VoiciD/System-for-recieving-geostationary-satellites-by-the-IAT-Groundstation/doc/Bilder/CW Basisband.png

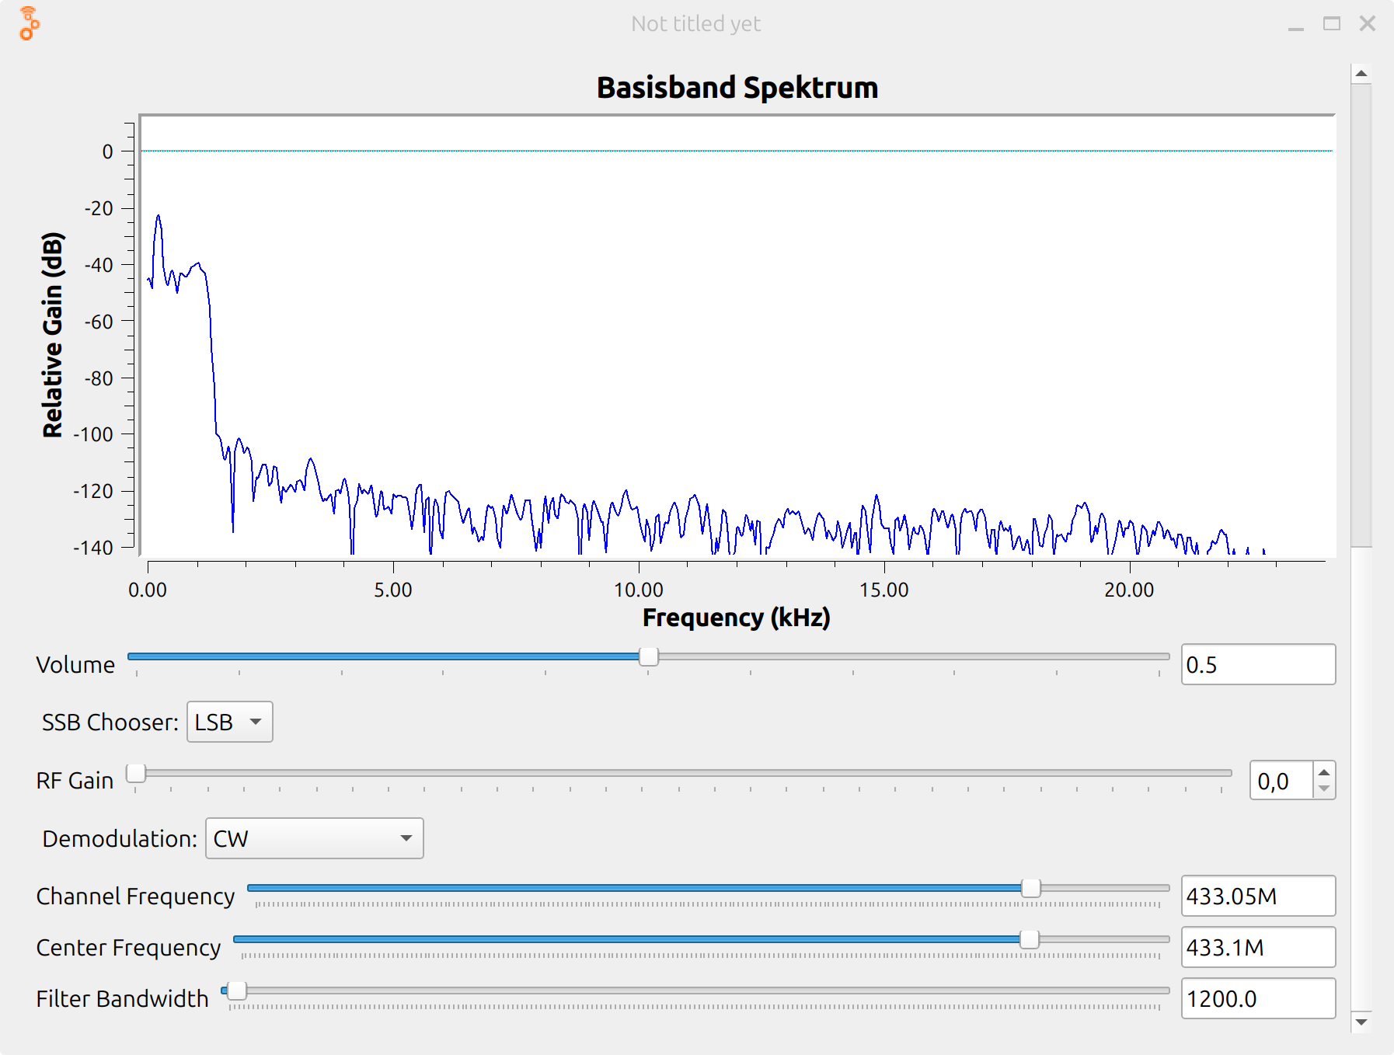
doc/Bilder/CW Basisband.png
