VoiciD/System-for-recieving-geostationary-satellites-by-the-IAT-Groundstation/doc/Bilder/Duobandfeed.jpg

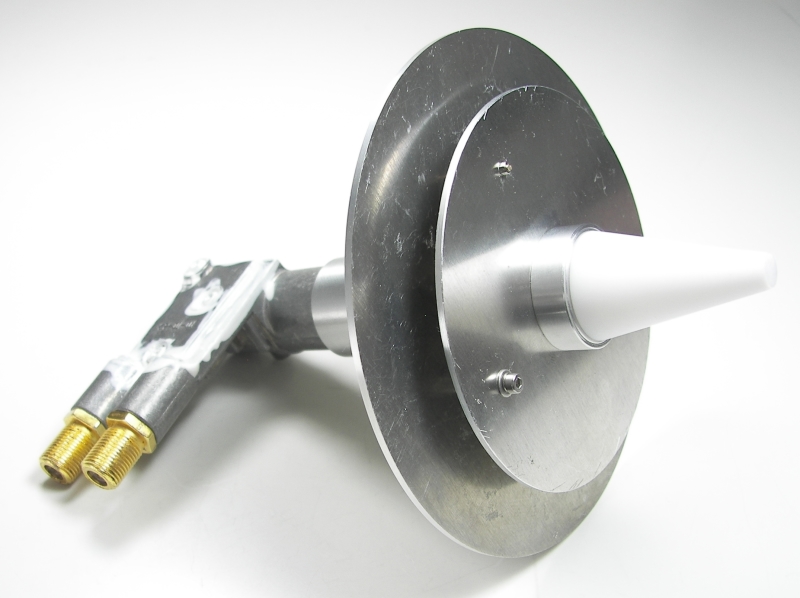
doc/Bilder/Duobandfeed.jpg
