VoiciD/System-for-recieving-geostationary-satellites-by-the-IAT-Groundstation/doc/Bilder/FM Radio.png

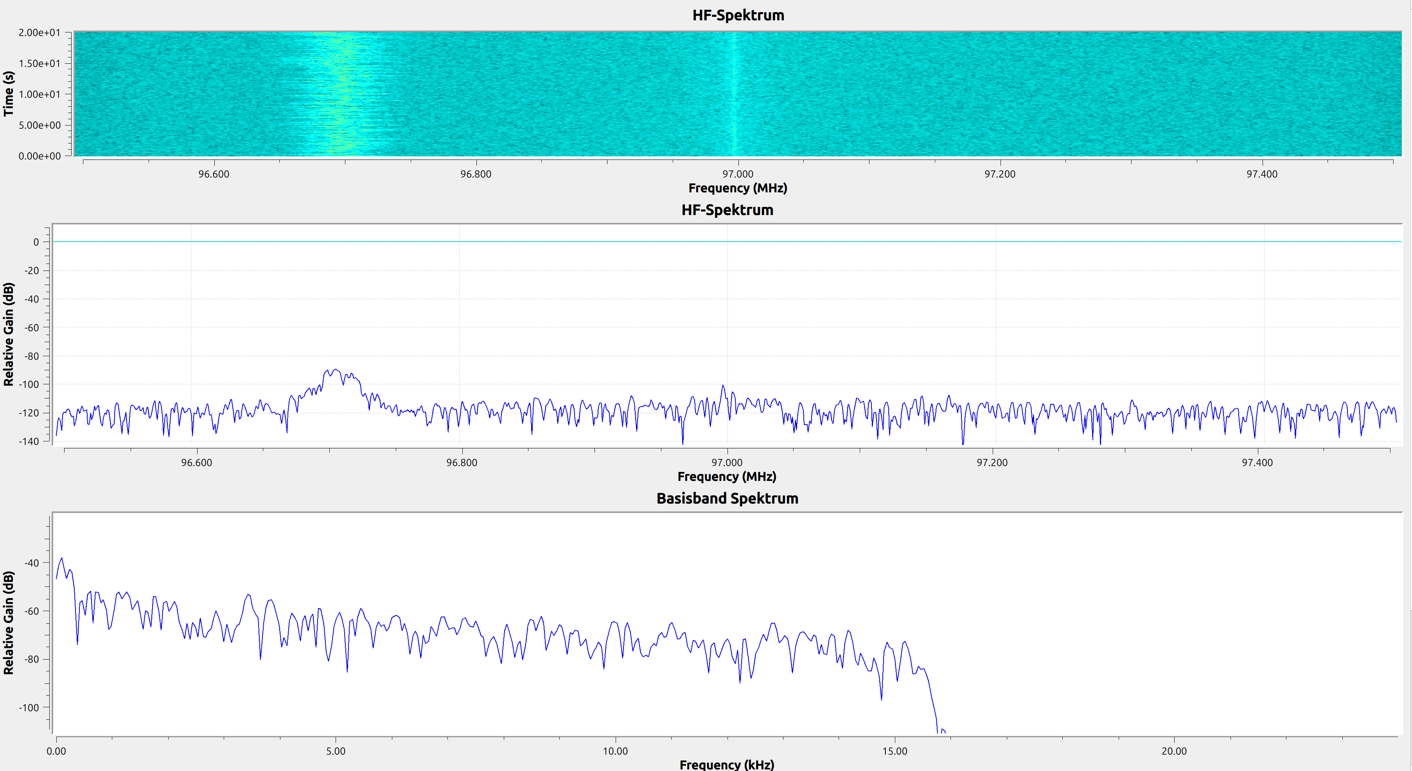
doc/Bilder/FM Radio.png
