VoiciD/System-for-recieving-geostationary-satellites-by-the-IAT-Groundstation/doc/Bilder/HF-Spektrum LSB.png

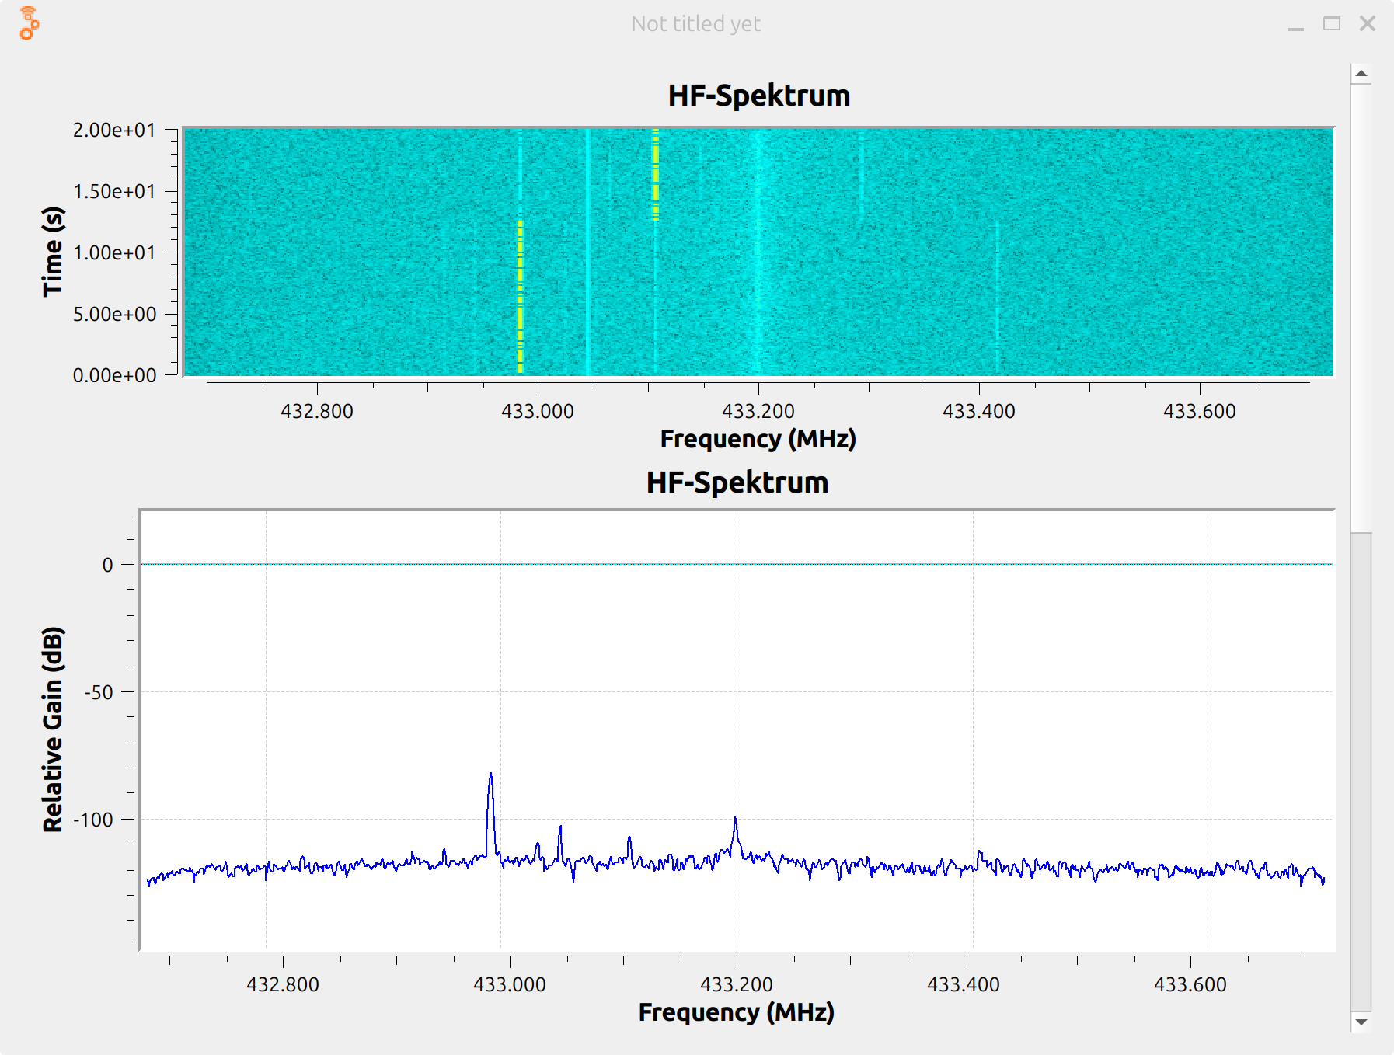
doc/Bilder/HF-Spektrum LSB.png
