VoiciD/System-for-recieving-geostationary-satellites-by-the-IAT-Groundstation/doc/Bilder/KU BT 10 REF.png

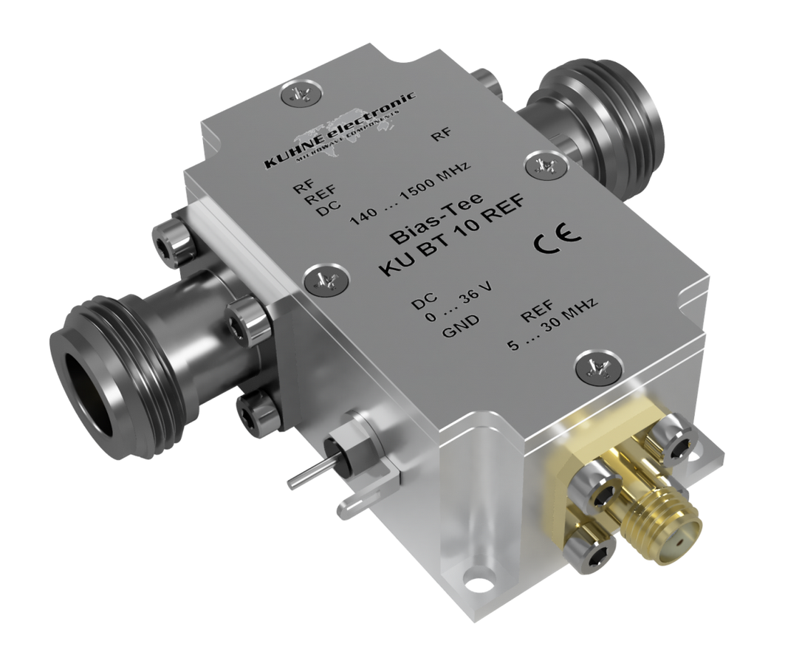
doc/Bilder/KU BT 10 REF.png
