VoiciD/System-for-recieving-geostationary-satellites-by-the-IAT-Groundstation/doc/Bilder/LinkBudget_lightRain.png

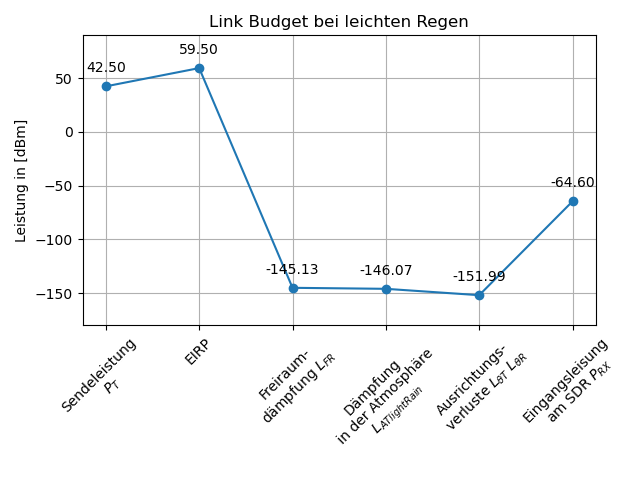
doc/Bilder/LinkBudget_lightRain.png
