VoiciD/System-for-recieving-geostationary-satellites-by-the-IAT-Groundstation/doc/Bilder/LSB Basisband.png

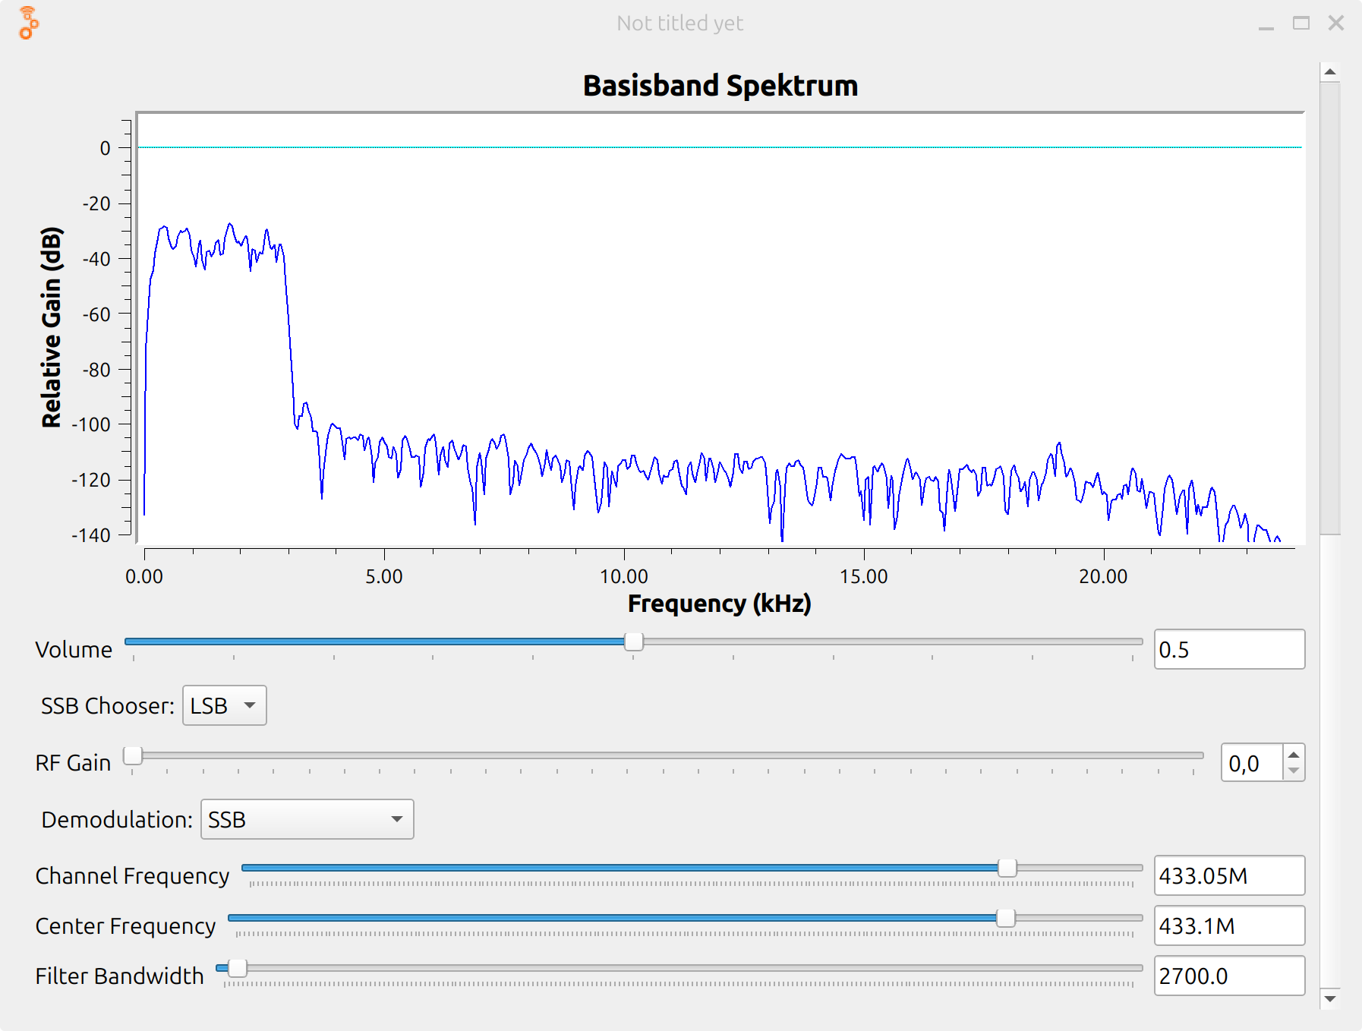
doc/Bilder/LSB Basisband.png
