VoiciD/System-for-recieving-geostationary-satellites-by-the-IAT-Groundstation/doc/Bilder/MKU LNC10 QO 100.png

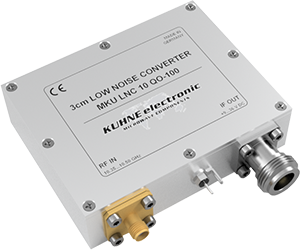
doc/Bilder/MKU LNC10 QO 100.png
