VoiciD/System-for-recieving-geostationary-satellites-by-the-IAT-Groundstation/Grafiken/Bilder/Aufgebaute Antenne.jpg

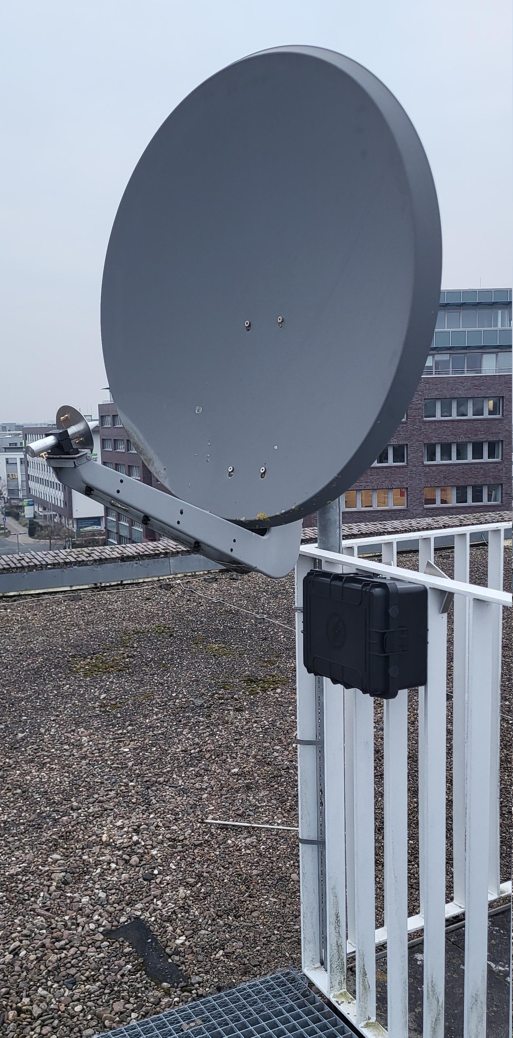
Grafiken/Bilder/Aufgebaute Antenne.jpg
