VoiciD/System-for-recieving-geostationary-satellites-by-the-IAT-Groundstation/Grafiken/Bilder/Gedruckter Feedhalter.jpg

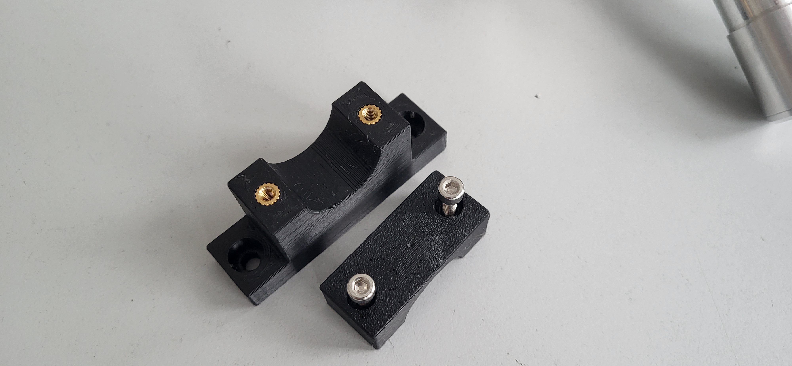
Grafiken/Bilder/Gedruckter Feedhalter.jpg
