VoiciD/System-for-recieving-geostationary-satellites-by-the-IAT-Groundstation/Grafiken/Bilder/Gelieferter Triplebandfeed.jpg

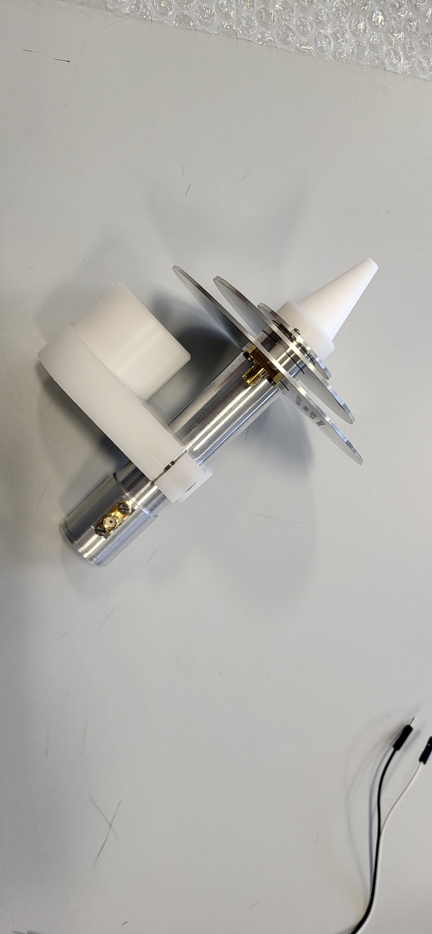
Grafiken/Bilder/Gelieferter Triplebandfeed.jpg
