VoiciD/System-for-recieving-geostationary-satellites-by-the-IAT-Groundstation/Grafiken/Bilder/LNC im Gehäuse.jpg

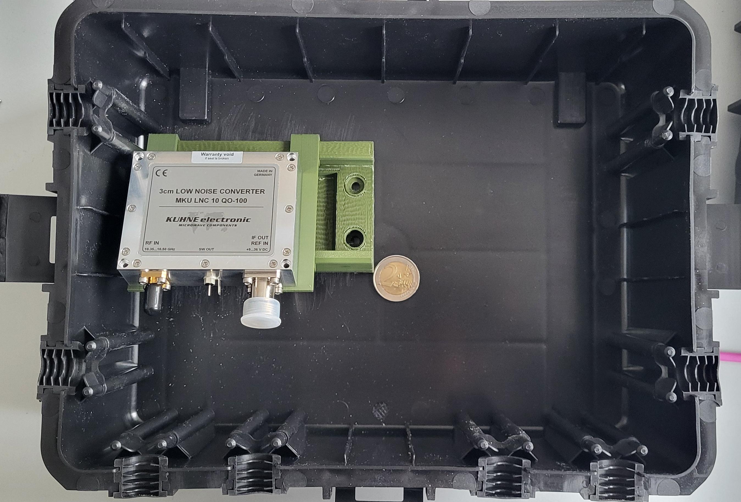
Grafiken/Bilder/LNC im Gehäuse.jpg
