VoiciD/System-for-recieving-geostationary-satellites-by-the-IAT-Groundstation/Grafiken/Bilder/RF-Switch und Patchfeld.jpg

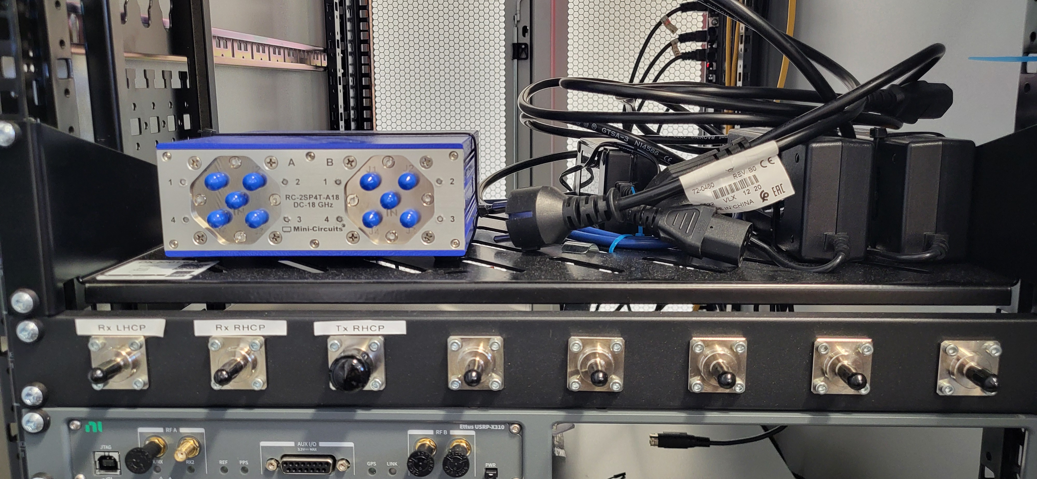
Grafiken/Bilder/RF-Switch und Patchfeld.jpg
