VoiciD/System-for-recieving-geostationary-satellites-by-the-IAT-Groundstation/Grafiken/Bilder/Vorhandene Antenne.jpg

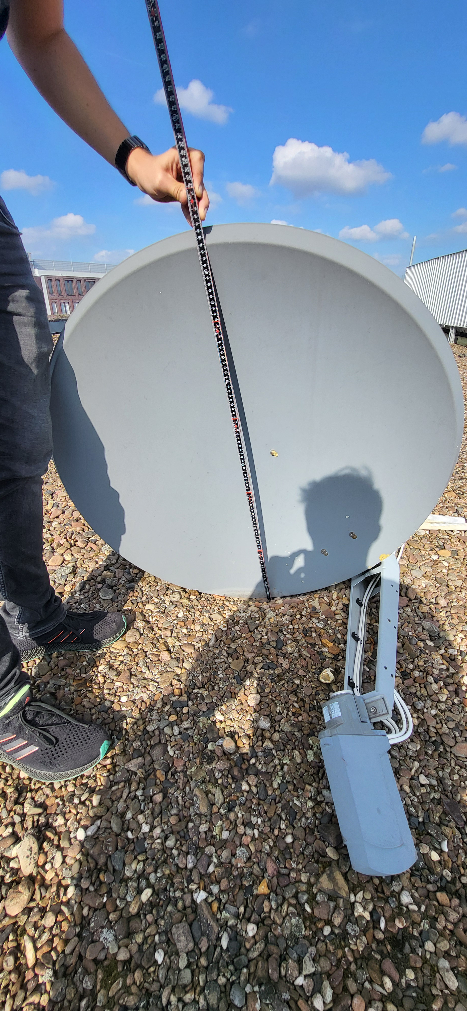
Grafiken/Bilder/Vorhandene Antenne.jpg
