VoiciD/System-for-recieving-geostationary-satellites-by-the-IAT-Groundstation/Grafiken/Messungen/Spektrum EsHail-2.PNG

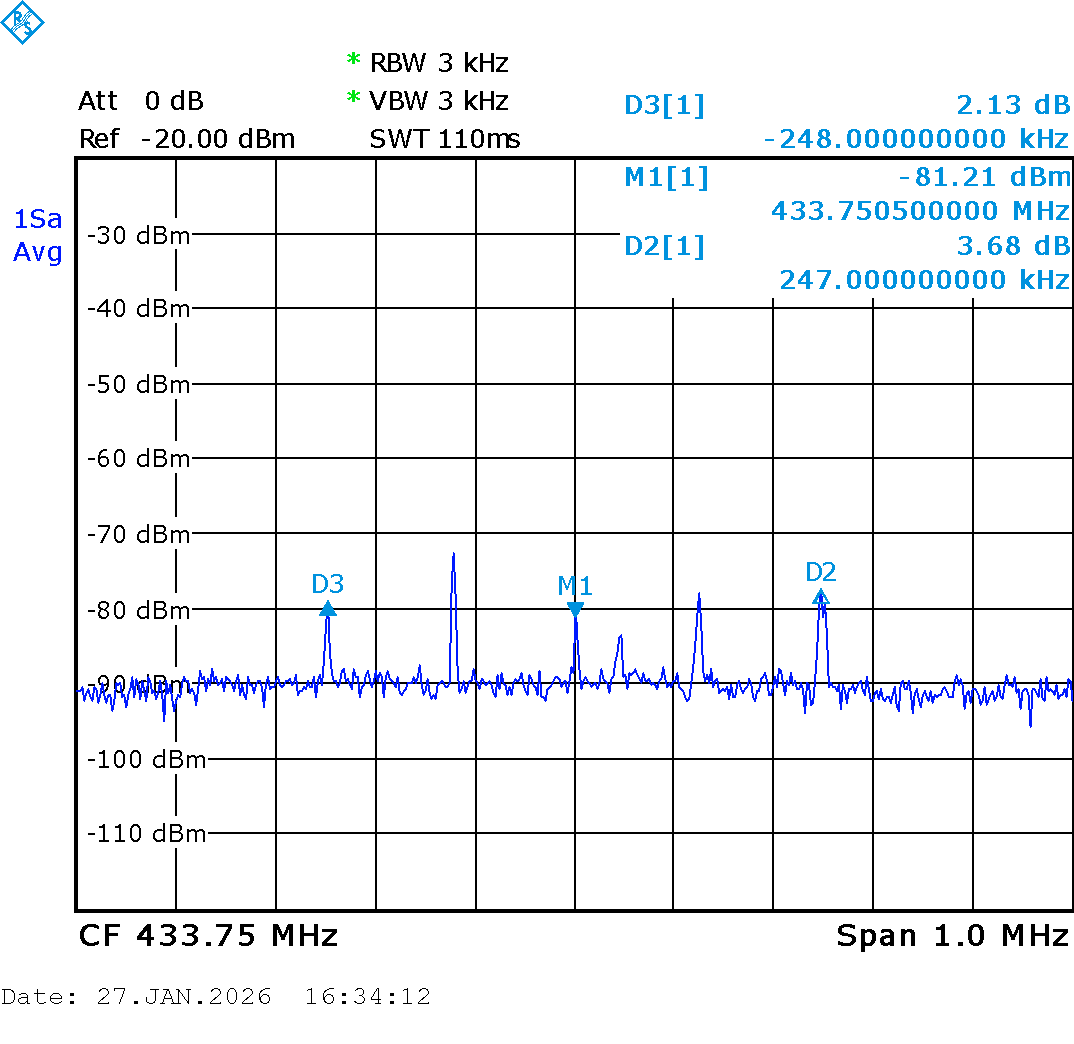
Grafiken/Messungen/Spektrum EsHail-2.PNG
