VoiciD/System-for-recieving-geostationary-satellites-by-the-IAT-Groundstation/Grafiken/Plots/Example SNR bad.png

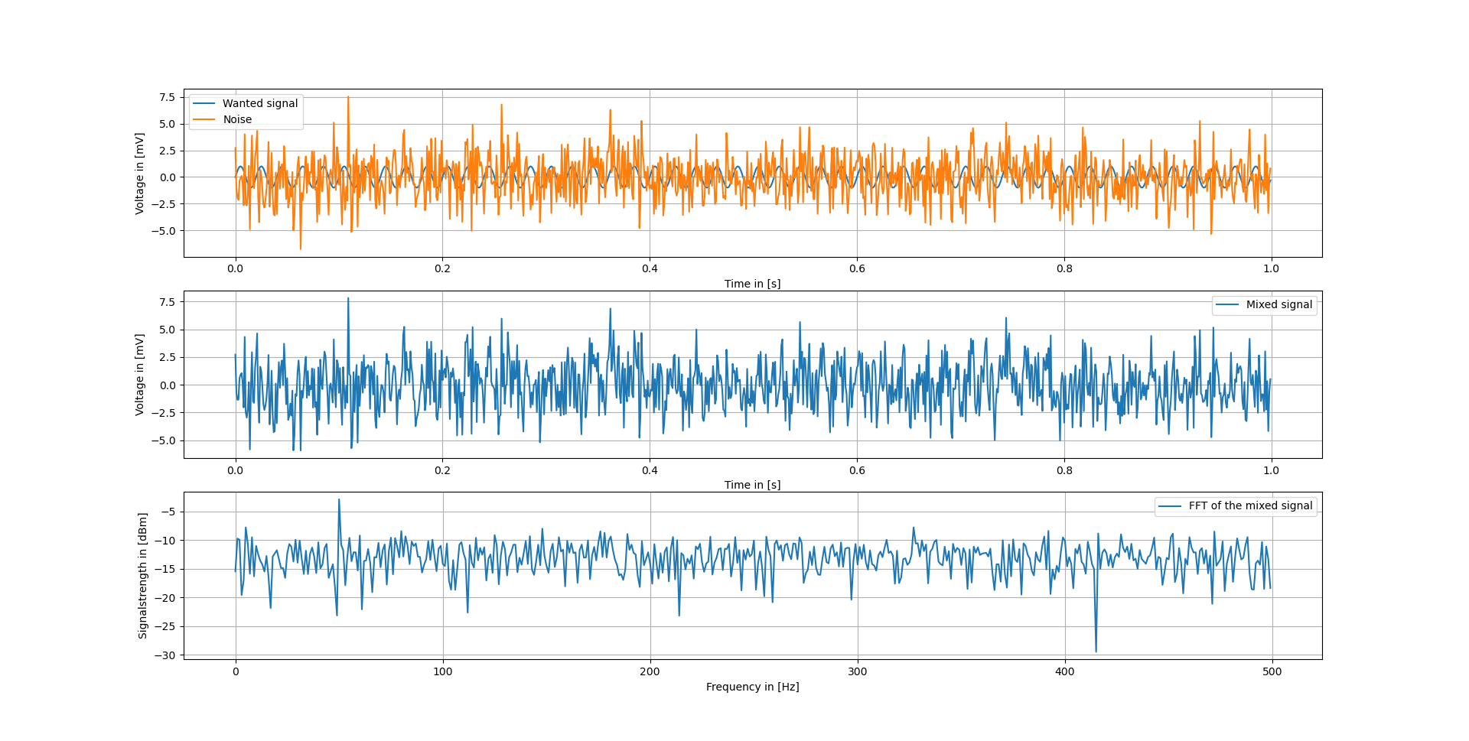
Grafiken/Plots/Example SNR bad.png
