VoiciD/System-for-recieving-geostationary-satellites-by-the-IAT-Groundstation/Grafiken/Plots/Example SNR good.png

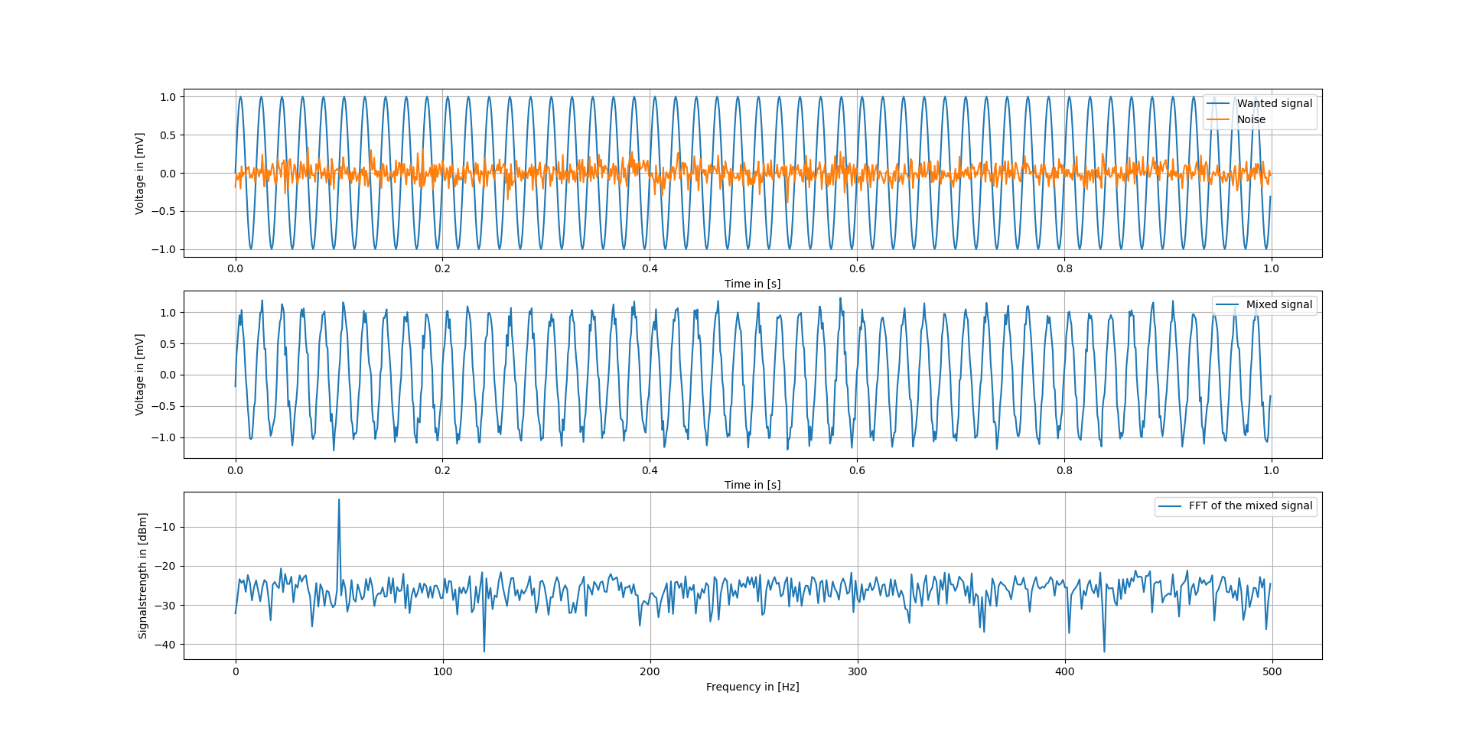
Grafiken/Plots/Example SNR good.png
