VoiciD/System-for-recieving-geostationary-satellites-by-the-IAT-Groundstation/Grafiken/Screenshots/Eingang.png

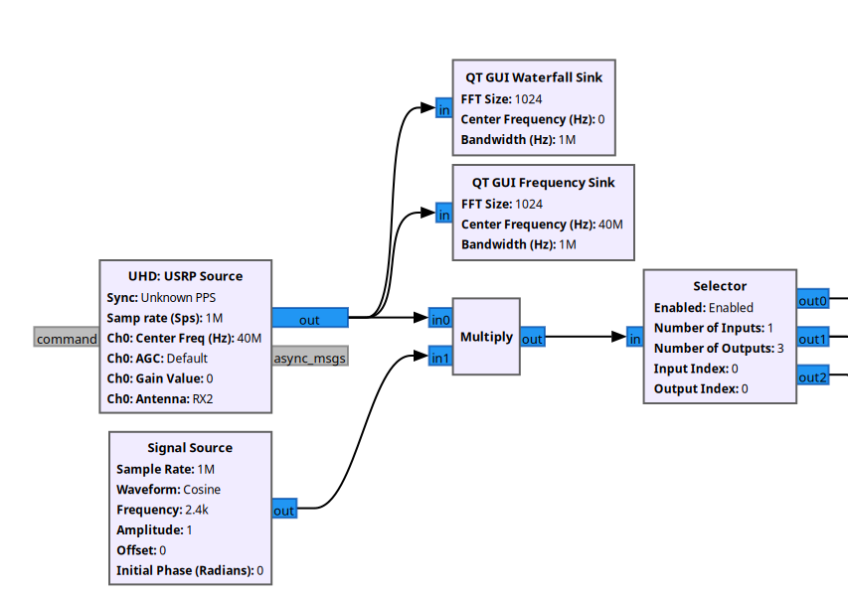
Grafiken/Screenshots/Eingang.png
