VoiciD/System-for-recieving-geostationary-satellites-by-the-IAT-Groundstation/Grafiken/Screenshots/Spektrum und Wasserfall.png

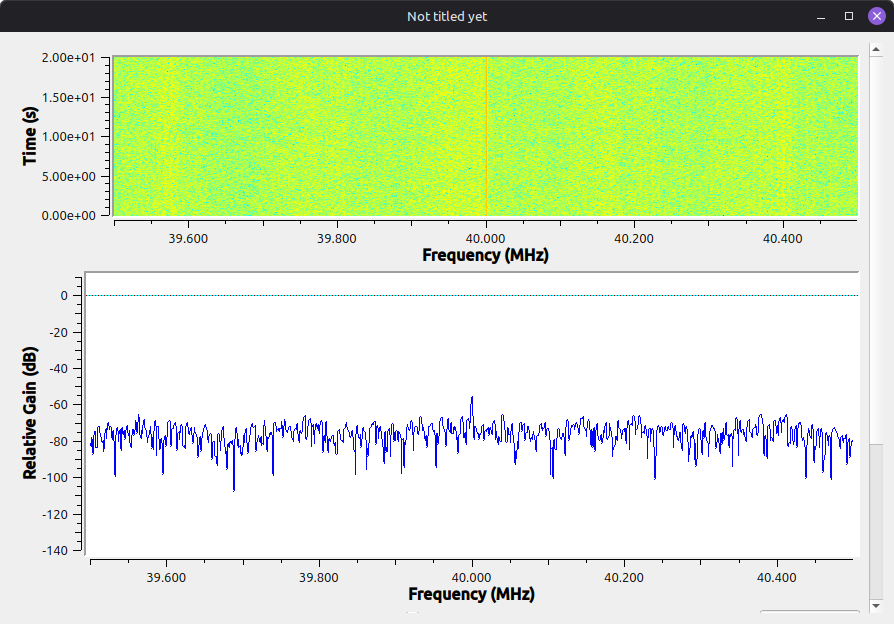
Grafiken/Screenshots/Spektrum und Wasserfall.png
