VoiciD/System-for-recieving-geostationary-satellites-by-the-IAT-Groundstation/Grafiken/Screenshots/USRP Source Block.png

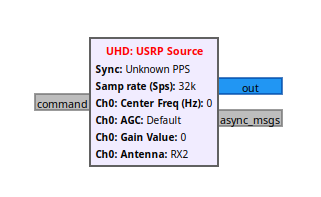
Grafiken/Screenshots/USRP Source Block.png
