VoiciD/System-for-recieving-geostationary-satellites-by-the-IAT-Groundstation/Grafiken/Skizzen/Skizze Downlink.png

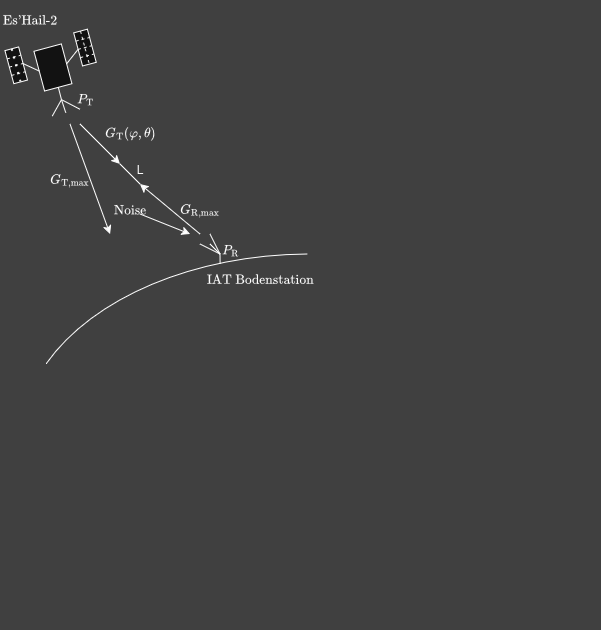
Grafiken/Skizzen/Skizze Downlink.png
